NirwanV/Five-Band-Equalizer/Version1/Simulations/Equilizer Stimulation.asc

+V: voltage; 15
-V: voltage; -15
BufferI: UniversalOpAmp2
C1: polcap; 10µ
C2: cap; 10n
C3: cap; 10n
C4: cap; 100n
C5: cap; 100n
C6: polcap; 10µ
C7: polcap; 10µ
C8: cap; 100n
C9: cap; 100n
C10: cap; 100n
C11: cap; 100n
C12: polcap; 10µ
C13: polcap; 10µ
C14: polcap; 10µ
C15: cap; 10n
C16: cap; 10n
C17: cap; 100n
C18: cap; 100n
C19: polcap; 10µ
C20: polcap; 10µ
C21: polcap; 10µ
C22: cap; 10n
C23: cap; 10n
C24: cap; 20n
C25: cap; 20n
C26: polcap; 10µ
C27: polcap; 10µ
C28: polcap; 10µ
C29: cap; 3.3n
C30: cap; 3.3n
C31: cap; 33n
C32: cap; 33n
C33: polcap; 10µ
C34: polcap; 10µ
C35: polcap; 10µ
R1: res; 1k
R2: res; 33k
R3: res; 150k
R4: res; 180k
R5: res; 15k
R6: res; 82k
R7: res; 270k
R8: res; 1k
R9: res; 1k
R10: res; 1k
R11: res; 1k
R12: res; 3.3k
R13: res; 12k
R14: res; 4.7k
R15: res; 1.5k
R16: res; 4.7k
R17: res; 1.5k
R18: res; 1k
R19: res; 1k
R20: res; 1k
R21: res; 1k
R22: res; 3.3k
R23: res; 10k
R24: res; 5.6k
R25: res; 0.82k
R26: res; 3.3k
R27: res; 2.2k
R28: res; 1k
R29: res; 1k
R30: res; 1k
R31: res; 1k
R32: res; 1.8k
R33: res; 5.6k
R34: res; 0.82k
R35: res; 1.8k
R36: res; 5.6k
R37: res; 0.82k
R38: res; 1k
R39: res; 1k
R40: res; 1k
R41: res; 1k
R42: res; 3.3k
R43: res; 10k
R44: res; 0.82k
R45: res; 0.56k
R46: res; 1.8k
R47: res; 0.15k
R48: res; 1k
R49: res; 1k
R50: res; 1k
R51: res; 1k
Source: voltage; ""; AC 1 0
U1: UniversalOpAmp2
U2: UniversalOpAmp2
U3: UniversalOpAmp2
U4: UniversalOpAmp2
U5: UniversalOpAmp2
U6: UniversalOpAmp2
U7: UniversalOpAmp2
U8: UniversalOpAmp2
U9: UniversalOpAmp2
U10: UniversalOpAmp2
U11: UniversalOpAmp2
U12: UniversalOpAmp2
U13: UniversalOpAmp2
U14: UniversalOpAmp2
U15: UniversalOpAmp2
U16: UniversalOpAmp2
Named nets: 0, VCC, -VCC
.ac dec 10000 1 100000
